MrBolas/WaterMe/Hardware/Microcontroller/photos/photo_2020-11-09_10-11-15.jpg

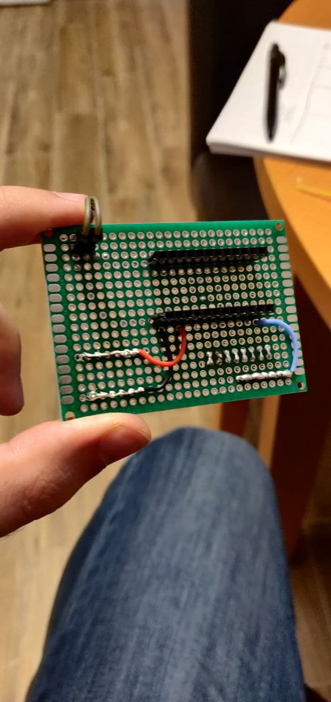
Hardware/Microcontroller/photos/photo_2020-11-09_10-11-15.jpg
