MrBolas/WaterMe/Hardware/Microcontroller/photos/photo_2020-11-09_10-12-27.jpg

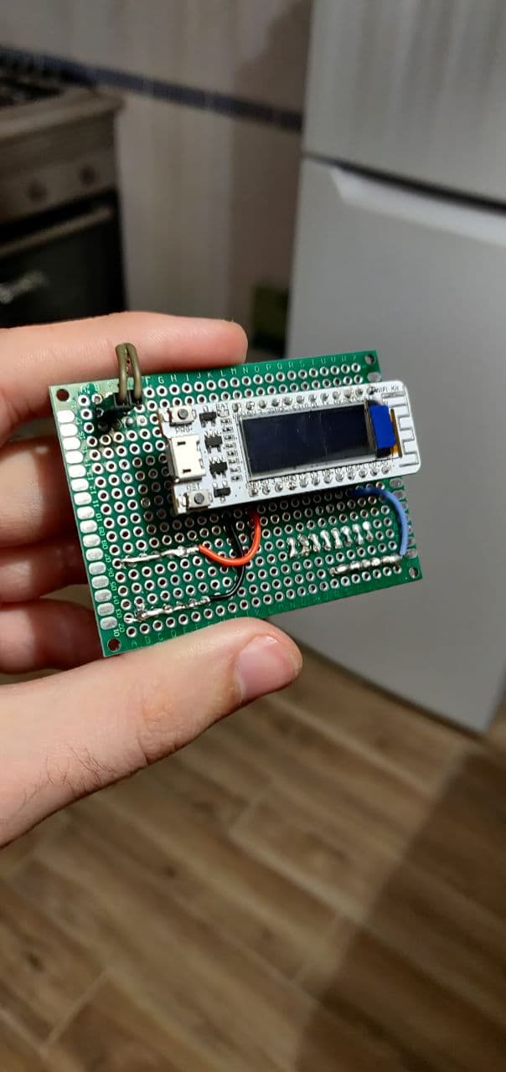
Hardware/Microcontroller/photos/photo_2020-11-09_10-12-27.jpg
