MrBolas/WaterMe/Hardware/Microcontroller/photos/photo_2020-11-09_10-12-33.jpg

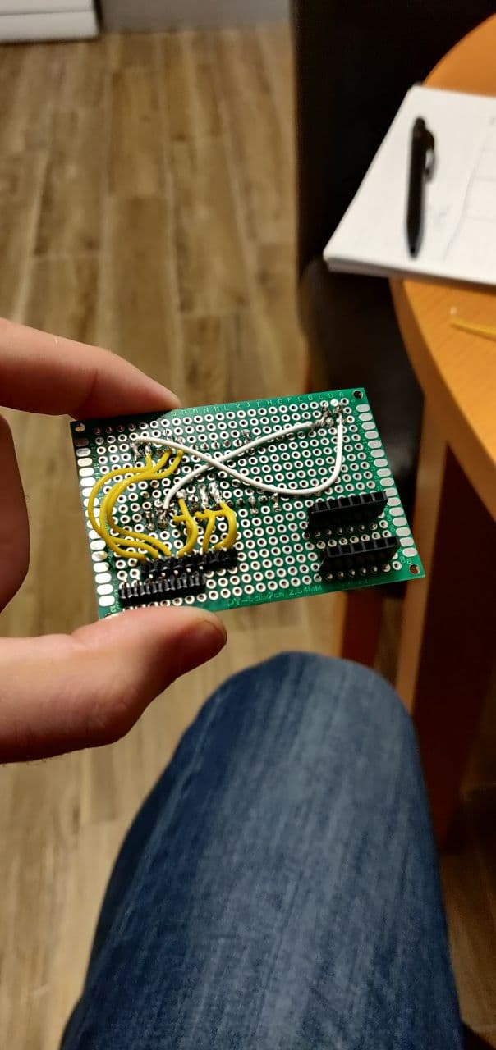
Hardware/Microcontroller/photos/photo_2020-11-09_10-12-33.jpg
